aplatonov2906-ai/dovetail-mount/out/diff_exact.png

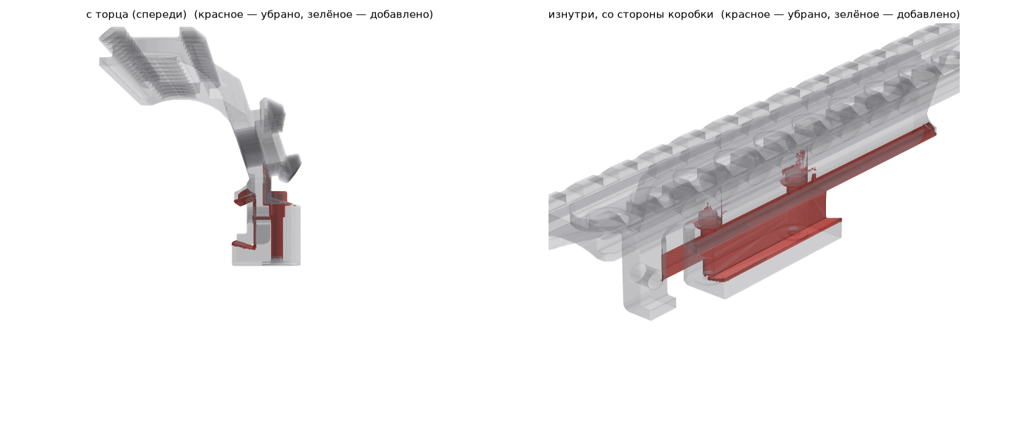
out/diff_exact.png
