aplatonov2906-ai/dovetail-mount/out/preview.png

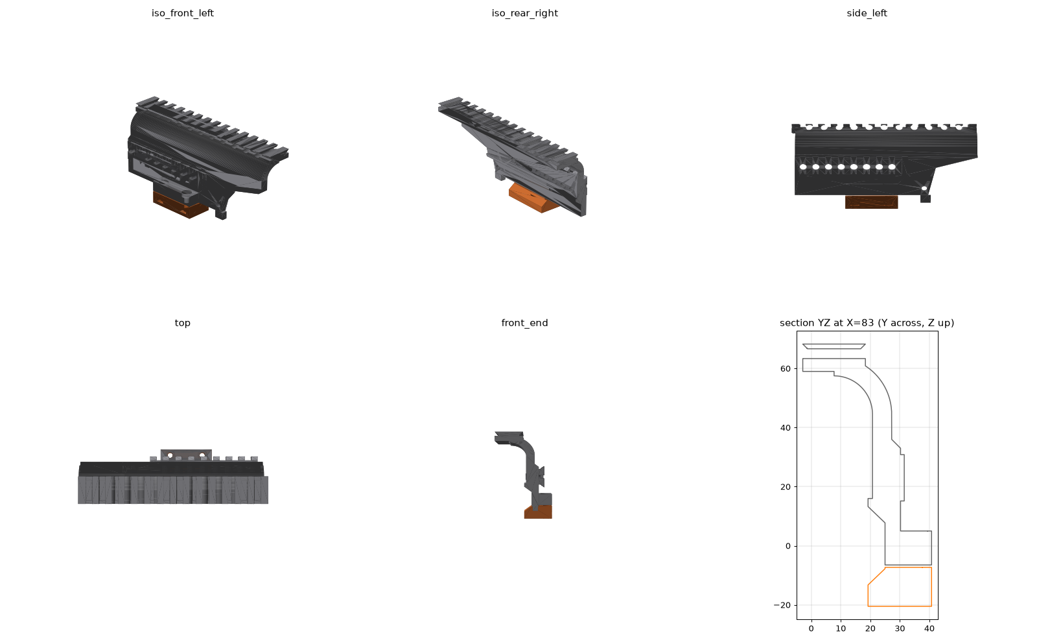
out/preview.png
