aplatonov2906-ai/dovetail-mount/out/preview_exact_clamp.png

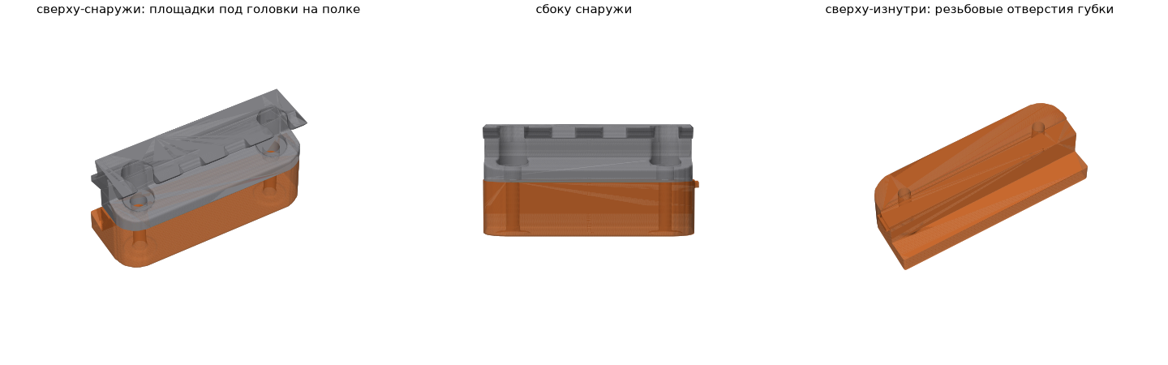
out/preview_exact_clamp.png
