aplatonov2906-ai/dovetail-mount/out/preview_exact_jaw.png

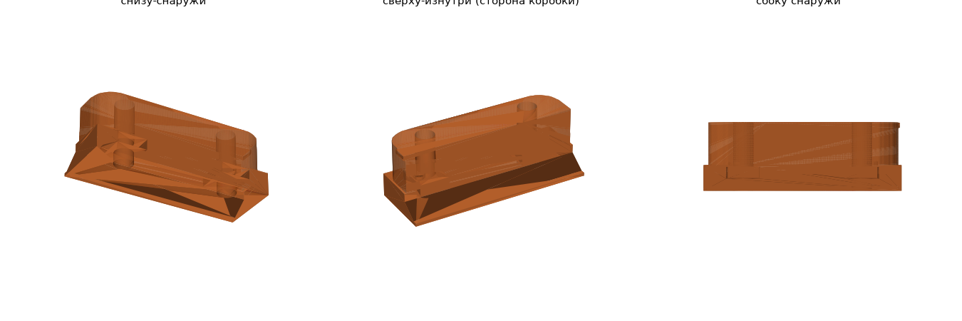
out/preview_exact_jaw.png
