aplatonov2906-ai/dovetail-mount/ref/2.jpg

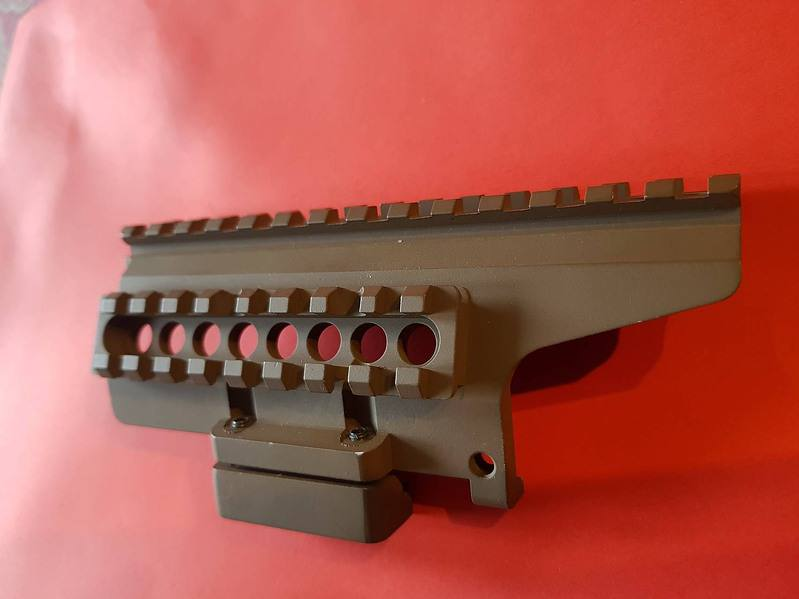
ref/2.jpg
