aplatonov2906-ai/dovetail-mount/ref/4.jpg

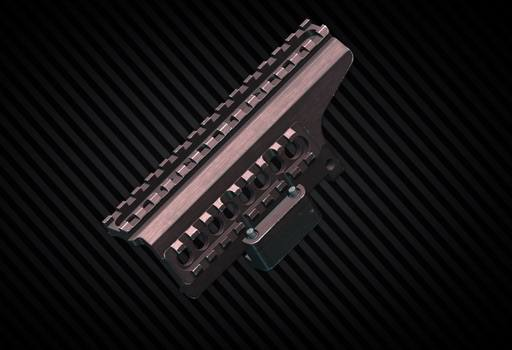
ref/4.jpg
