aplatonov2906-ai/dovetail-mount/ref/6.jpg

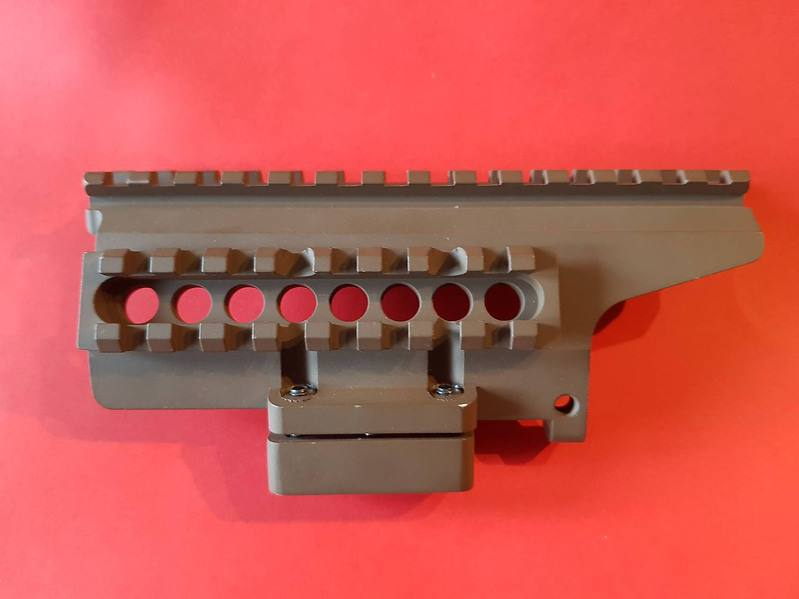
ref/6.jpg
