aplatonov2906-ai/dovetail-mount/ref/10.jpg

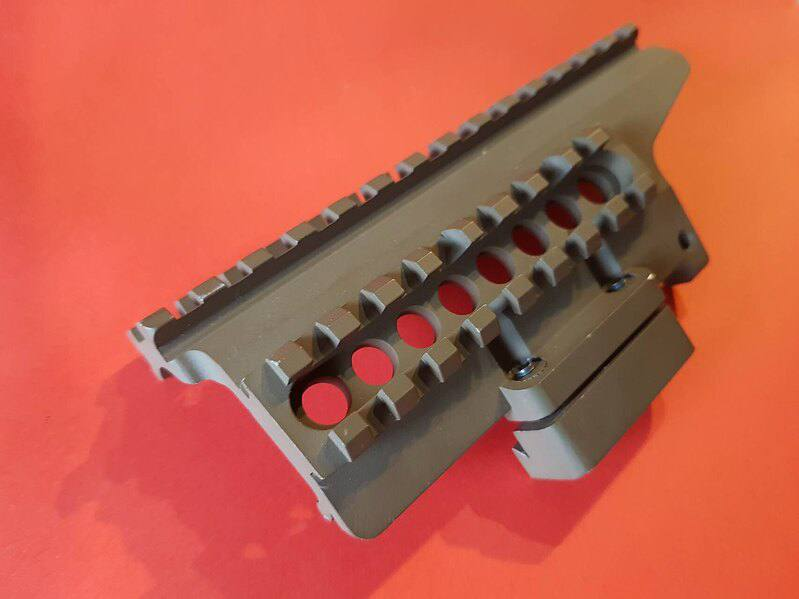
ref/10.jpg
