aplatonov2906-ai/dovetail-mount/ref/caliper_cover_width_36_5.jpg

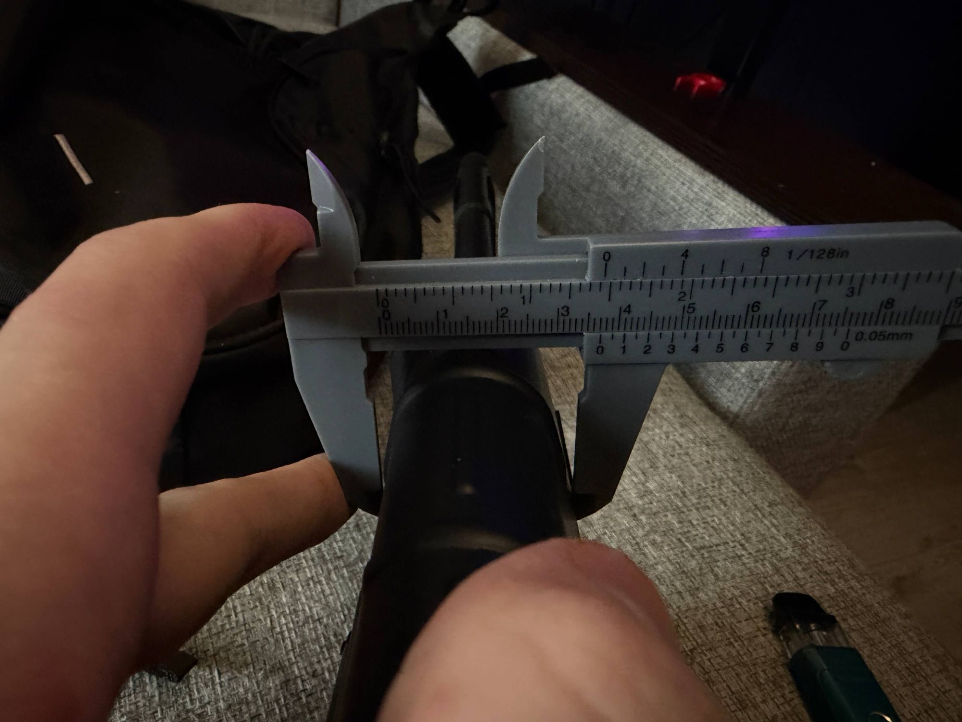
ref/caliper_cover_width_36_5.jpg
