aplatonov2906-ai/dovetail-mount/ref/caliper_lower_width_44.jpg

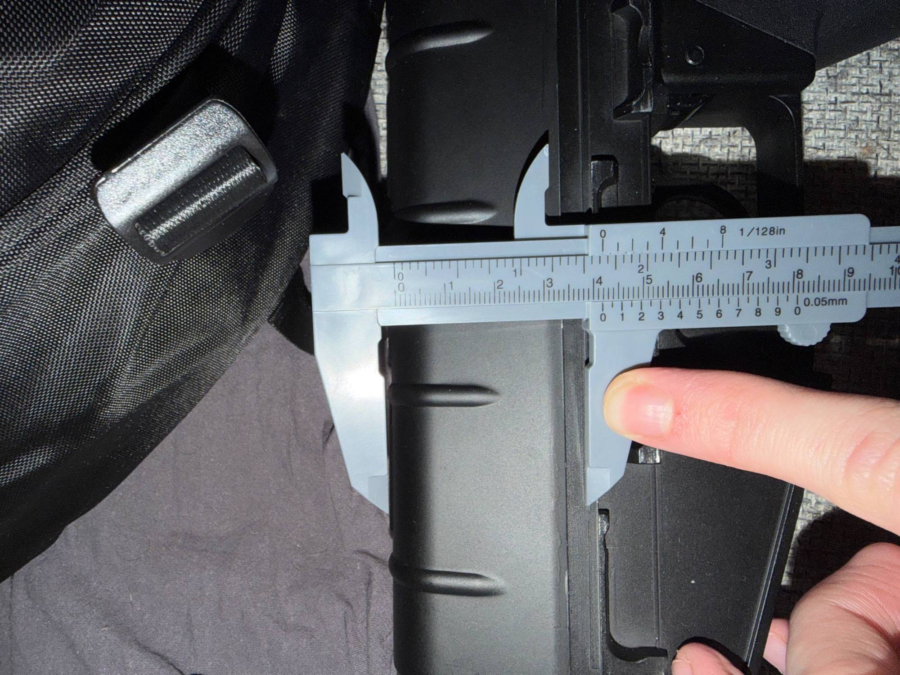
ref/caliper_lower_width_44.jpg
