aplatonov2906-ai/dovetail-mount/ref/caliper_rail_depth_5_5.jpg

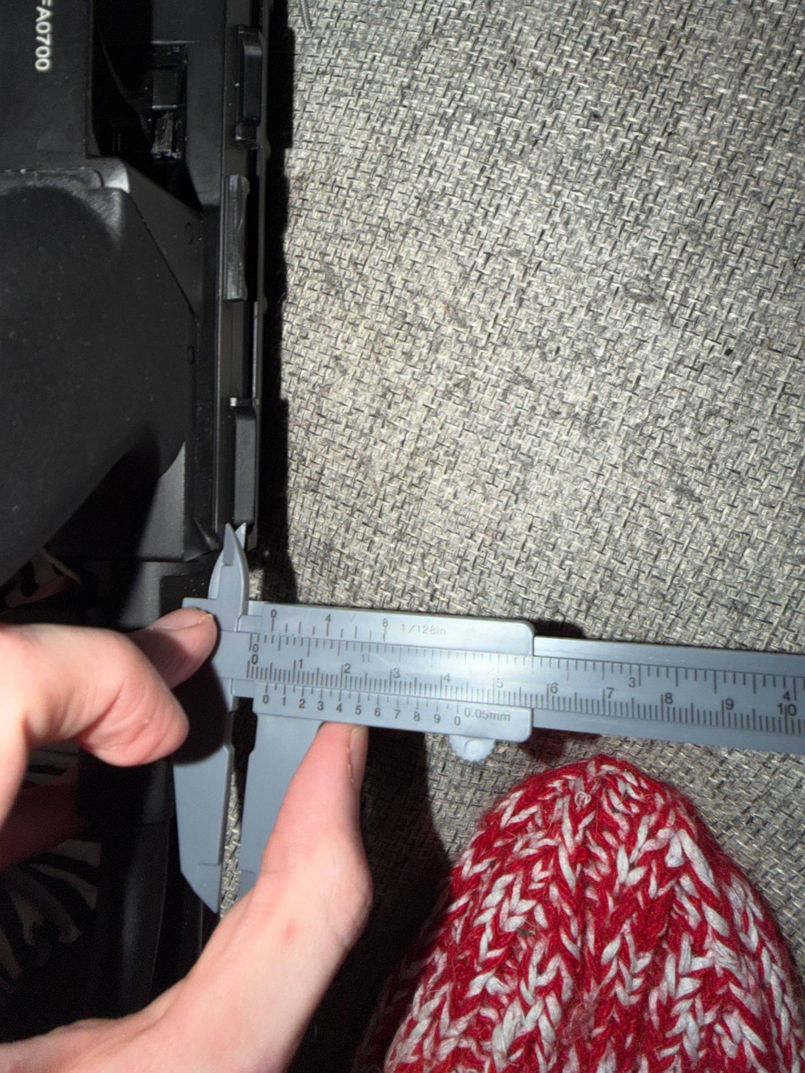
ref/caliper_rail_depth_5_5.jpg
