aplatonov2906-ai/dovetail-mount/ref/frame_side.jpg

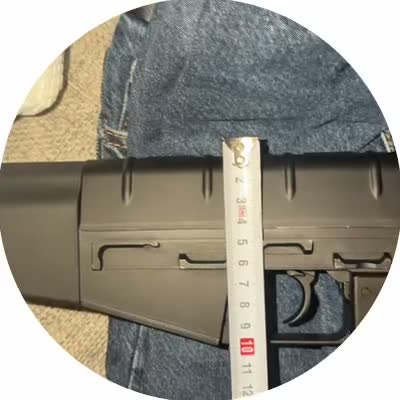
ref/frame_side.jpg
