aplatonov2906-ai/dovetail-mount/ref/proto_lower_sections.png

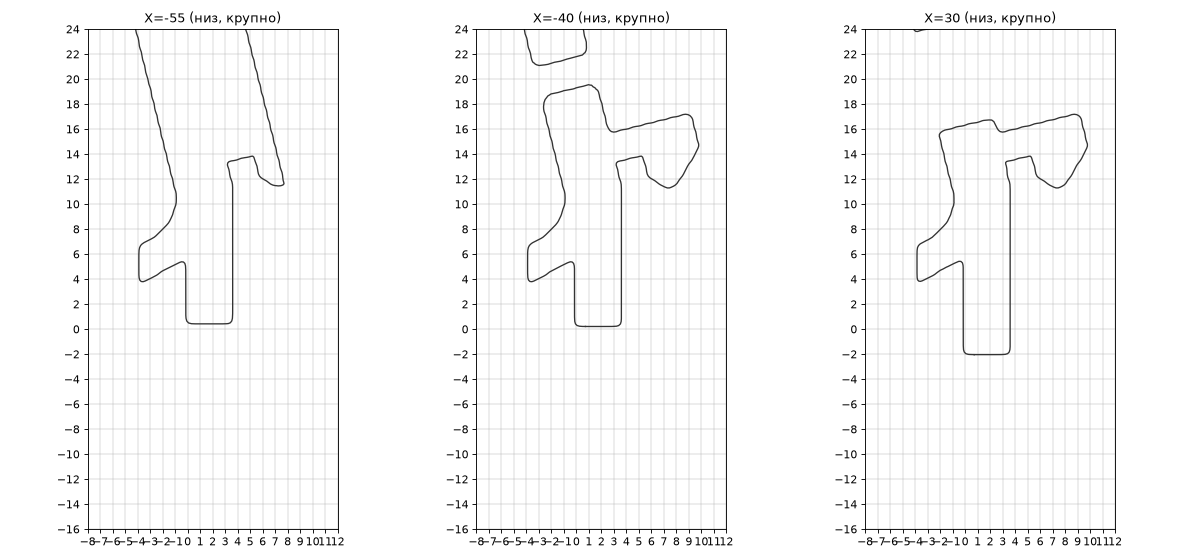
ref/proto_lower_sections.png
