aplatonov2906-ai/dovetail-mount/ref/proto_silhouette.png

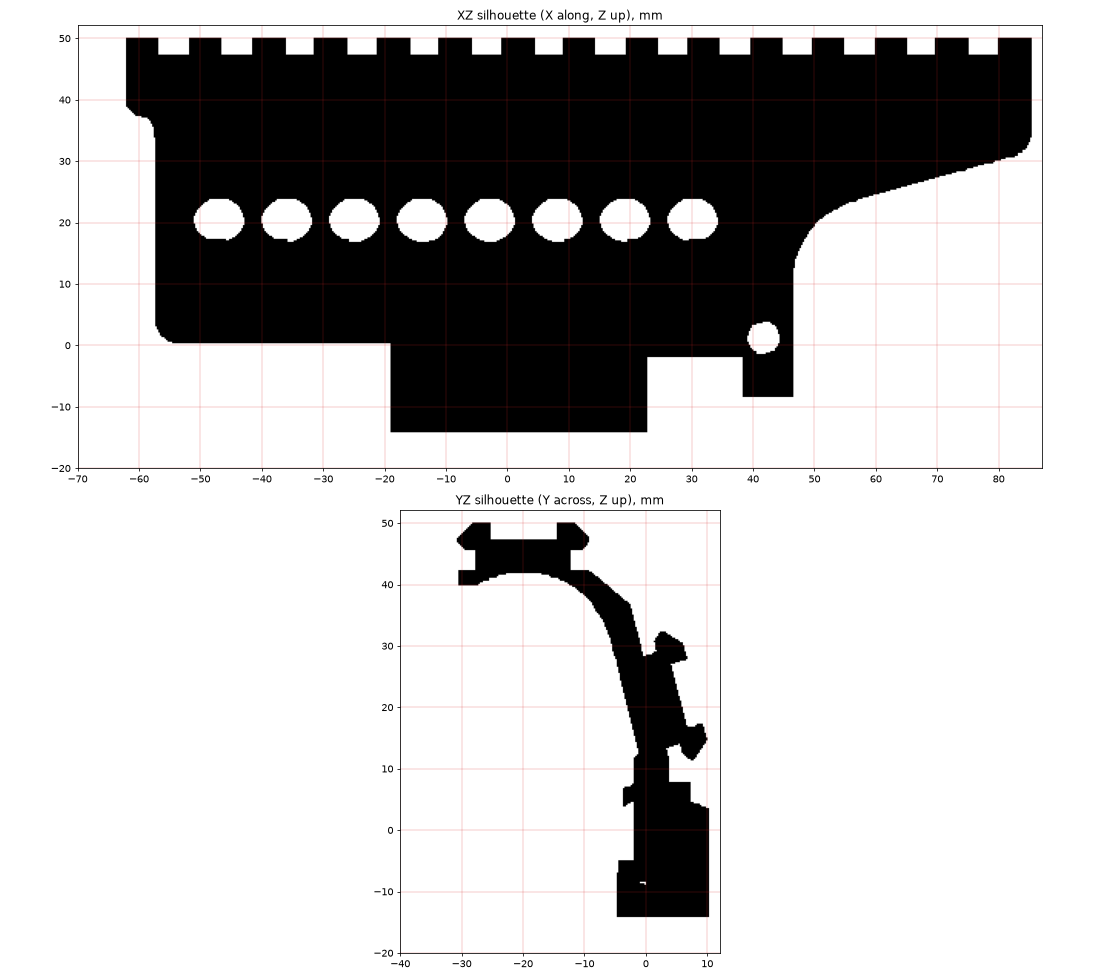
ref/proto_silhouette.png
