aplatonov2906-ai/dovetail-mount/ref/proto_solid_views.png

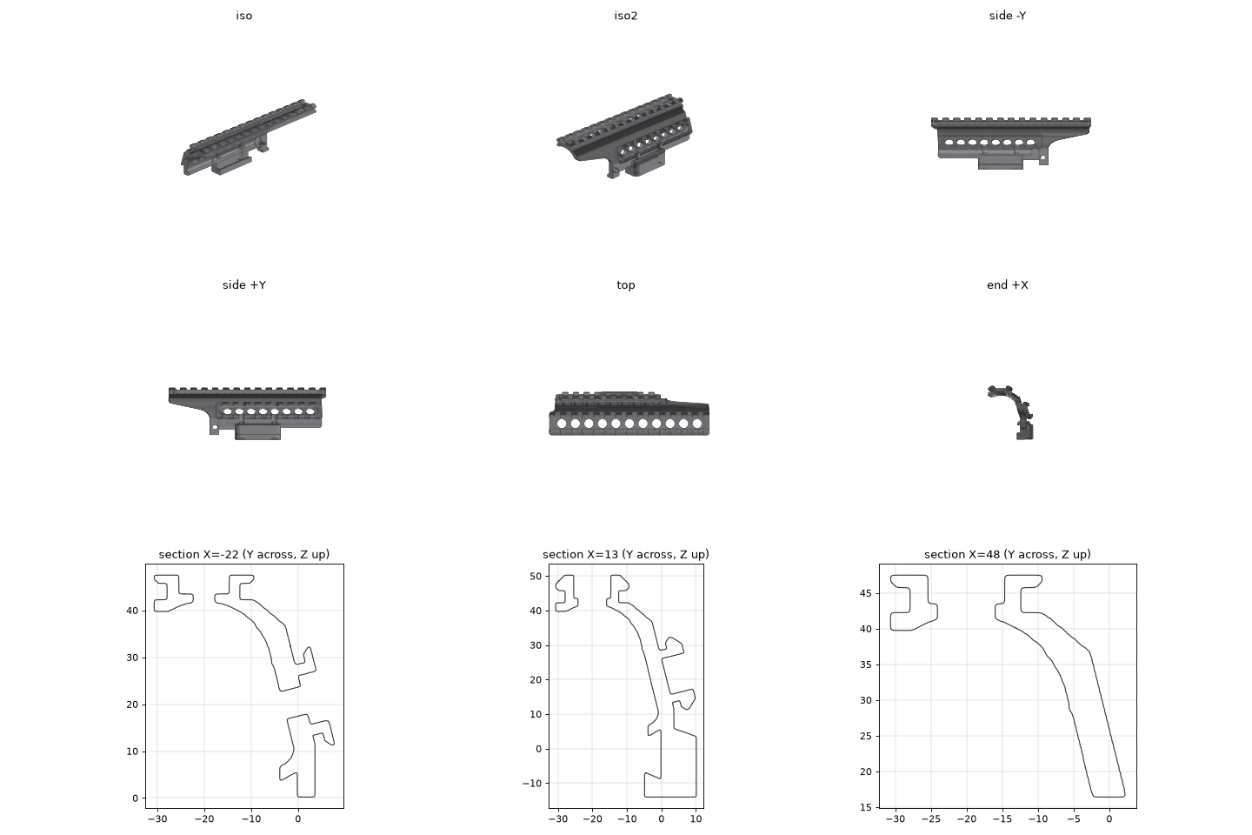
ref/proto_solid_views.png
