aplatonov2906-ai/dovetail-mount/ref/rail_end.jpg

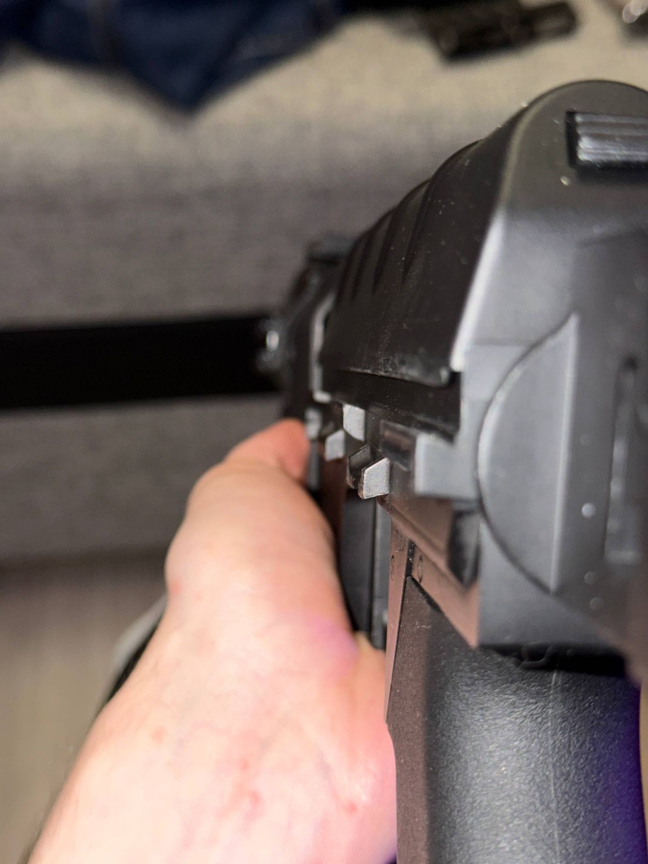
ref/rail_end.jpg
