aplatonov2906-ai/dovetail-mount/ref/rail_side_seam.jpg

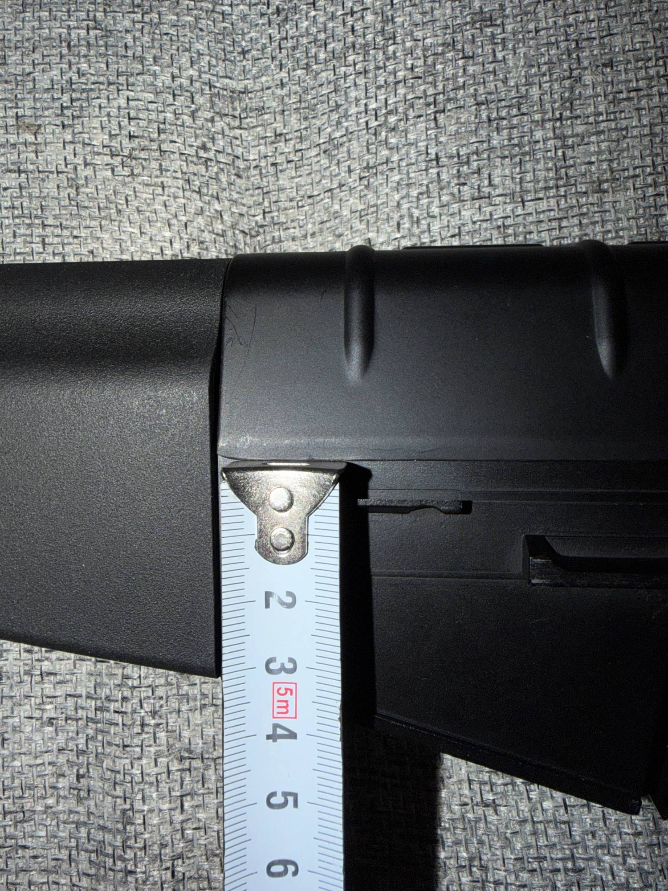
ref/rail_side_seam.jpg
