aplatonov2906-ai/dovetail-mount/ref/rail_side_top.jpg

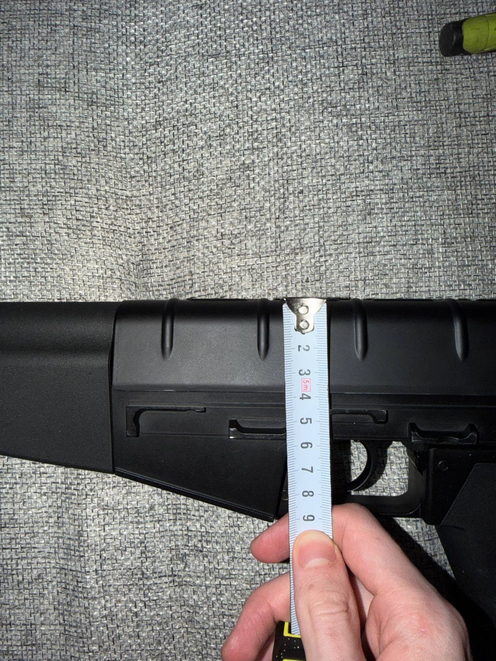
ref/rail_side_top.jpg
