aplatonov2906-ai/dovetail-mount/ref/measure.png

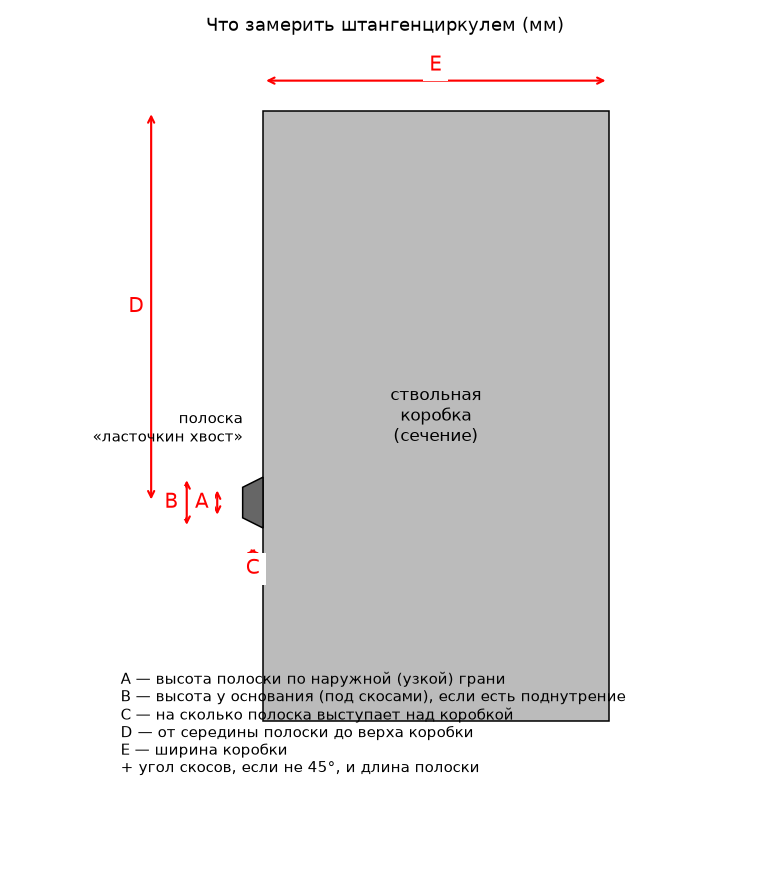
ref/measure.png
